bullestock/SmartPendantHardware/kicad/frame.scad

difference(){ translate([0, 0, -0.995]) linear_extrude(height=2.6) polygon(points=[[-44.378709539066506, -47.255384540973324], [-44.378709539066506, 41.744615459026676], [110.6212904609335, 41.744615459026676], [110.6212904609335, -47.255384540973324]]); 
union() {
 linear_extrude(height=10) offset(r=0.1) polygon(points=[[34.621290460933494, 26.744615459026676], [34.621595070620714, 26.70971064615211], [34.6225088068953, 26.674816465621674], [34.62403139142435, 26.639943546540785], [34.62616236041384, 26.605102511538426], [34.62890106475001, 26.57030397353136], [34.632246670196935, 26.535558532491372], [34.63619815765085, 26.50087677221638], [34.64075432345035, 26.466269257106546], [34.64591377974321, 26.431746528946213], [34.65167495490908, 26.397319103692816], [34.65803609403815, 26.362997468273583], [34.66499525946588, 26.328792077391157], [34.67255033136303, 26.294713350338945], [34.68069900838151, 26.260771667827342], [34.68943880835536, 26.226977368821636], [34.698767069056856, 26.193340747392675], [34.70868094900743, 26.159872049581203], [34.71917742834319, 26.126581470276783], [34.73025330973485, 26.093479150112366], [34.74190521936168, 26.060575172375337], [34.75412960793909, 26.027879559936075], [34.76692275179991, 25.995402272194852], [34.78028075402861, 25.963153202048126], [34.7941995456483, 25.931142172875077], [34.80867488686019, 25.89937893554528], [34.82370236833515, 25.867873165448522], [34.839277412556754, 25.836634459547582], [34.85539527521564, 25.805672333454893], [34.87205104665469, 25.774996218534], [34.889239653364626, 25.744615459026676], [34.90695585952926, 25.714539309206565], [34.92519426862063, 25.68477693056027], [34.94394932504264, 25.65533738899662], [34.96321531582342, 25.62622965208518], [34.9829863723555, 25.597462586324582], [35.00325647218361, 25.56904495444173], [35.02401944083891, 25.540985412722577], [35.04526895372004, 25.513292508375358], [35.06699853801956, 25.485974676927], [35.08920157469555, 25.459040239653596], [35.11187130048796, 25.43249740104566], [35.13500080997869, 25.406354246308958], [35.158583057695154, 25.38061873890168], [35.182610860256204, 25.355298718108685], [35.20707689856039, 25.330401896653584], [35.2319737200155, 25.305935858349372], [35.25729374080851, 25.281908055788335], [35.28302924821577, 25.258325808071888], [35.30917240295247, 25.23519629858113], [35.33571524156042, 25.21252657278872], [35.36264967883383, 25.190323536112736], [35.38996751028219, 25.16859395181323], [35.41766041462941, 25.147344438932087], [35.44571995634854, 25.126581470276783], [35.4741375882314, 25.106311370448694], [35.502904653992005, 25.086540313916593], [35.532012390903446, 25.067274323135827], [35.561451932467094, 25.048519266713825], [35.59121431111339, 25.03028085762245], [35.621290460933494, 25.0125646514578], [35.65167122044082, 24.995376044747886], [35.682347335361726, 24.978720273308824], [35.7133094614544, 24.962602410649943], [35.74454816735533, 24.947027366428344], [35.776053937452104, 24.931999884953377], [35.80781717478189, 24.91752454374147], [35.83982820395494, 24.9036057521218], [35.872077274101656, 24.8902477498931], [35.9045545618429, 24.877454606032273], [35.937250174282156, 24.865230217454858], [35.97015415201918, 24.853578307828045], [36.00325647218361, 24.84250242643637], [36.036547051488014, 24.832005947100605], [36.0700157492995, 24.822092067150038], [36.10365237072844, 24.812763806448537], [36.137446669734146, 24.804024006474684], [36.17138835224577, 24.79587532945621], [36.20546707929799, 24.788320257559064], [36.23967247018041, 24.78136109213135], [36.27399410559963, 24.774999953002258], [36.308421530853025, 24.7692387778364], [36.342944259013365, 24.764079321543534], [36.37755177412319, 24.759523155744034], [36.41223353439818, 24.75557166829013], [36.446978975438185, 24.752226062843185], [36.48177751344525, 24.749487358507025], [36.51661854844761, 24.747356389517527], [36.55149146752848, 24.745833804988486], [36.58638564805892, 24.744920068713895], [36.621290460933494, 24.744615459026676], [36.621290460933494, 24.744615459026676], [65.6212904609335, 24.744615459026676], [65.65619527380807, 24.744920068713895], [65.69108945433851, 24.745833804988486], [65.72596237341938, 24.747356389517527], [65.76080340842174, 24.749487358507025], [65.7956019464288, 24.752226062843185], [65.8303473874688, 24.75557166829013], [65.8650291477438, 24.759523155744034], [65.89963666285362, 24.764079321543534], [65.93415939101396, 24.7692387778364], [65.96858681626736, 24.774999953002258], [66.00290845168658, 24.78136109213135], [66.037113842569, 24.788320257559064], [66.07119256962122, 24.79587532945621], [66.10513425213284, 24.804024006474684], [66.13892855113855, 24.812763806448537], [66.17256517256749, 24.822092067150038], [66.20603387037897, 24.832005947100605], [66.23932444968338, 24.84250242643637], [66.27242676984781, 24.853578307828045], [66.30533074758483, 24.865230217454858], [66.33802636002409, 24.877454606032273], [66.37050364776533, 24.8902477498931], [66.40275271791205, 24.9036057521218], [66.4347637470851, 24.91752454374147], [66.46652698441488, 24.931999884953377], [66.49803275451166, 24.947027366428344], [66.52927146041259, 24.962602410649943], [66.56023358650526, 24.978720273308824], [66.59090970142617, 24.995376044747886], [66.6212904609335, 25.0125646514578], [66.6513666107536, 25.03028085762245], [66.6811289893999, 25.048519266713825], [66.71056853096354, 25.067274323135827], [66.73967626787498, 25.086540313916593], [66.76844333363559, 25.106311370448694], [66.79686096551845, 25.126581470276783], [66.82492050723758, 25.147344438932087], [66.8526134115848, 25.16859395181323], [66.87993124303316, 25.190323536112736], [66.90686568030657, 25.21252657278872], [66.93340851891452, 25.23519629858113], [66.95955167365122, 25.258325808071888], [66.98528718105848, 25.281908055788335], [67.01060720185149, 25.305935858349372], [67.0355040233066, 25.330401896653584], [67.05997006161078, 25.355298718108678], [67.08399786417183, 25.38061873890168], [67.1075801118883, 25.406354246308958], [67.13070962137903, 25.43249740104566], [67.15337934717144, 25.459040239653596], [67.17558238384743, 25.485974676927], [67.19731196814695, 25.513292508375358], [67.21856148102808, 25.540985412722577], [67.23932444968338, 25.56904495444173], [67.25959454951149, 25.597462586324582], [67.27936560604357, 25.62622965208518], [67.29863159682435, 25.65533738899662], [67.31738665324636, 25.68477693056027], [67.33562506233773, 25.714539309206565], [67.35334126850236, 25.744615459026676], [67.3705298752123, 25.774996218534], [67.38718564665135, 25.805672333454893], [67.40330350931023, 25.836634459547582], [67.41887855353184, 25.867873165448522], [67.4339060350068, 25.89937893554528], [67.44838137621869, 25.931142172875077], [67.46230016783838, 25.963153202048126], [67.47565817006708, 25.995402272194852], [67.4884513139279, 26.027879559936075], [67.5006757025053, 26.060575172375337], [67.51232761213214, 26.093479150112366], [67.5234034935238, 26.126581470276783], [67.53389997285956, 26.159872049581203], [67.54381385281013, 26.193340747392675], [67.55314211351163, 26.226977368821636], [67.56188191348548, 26.260771667827342], [67.57003059050396, 26.294713350338945], [67.5775856624011, 26.328792077391157], [67.58454482782884, 26.362997468273583], [67.5909059669579, 26.397319103692816], [67.59666714212378, 26.431746528946213], [67.60182659841664, 26.466269257106546], [67.60638276421614, 26.50087677221638], [67.61033425167005, 26.535558532491372], [67.61367985711698, 26.57030397353136], [67.61641856145314, 26.605102511538426], [67.61854953044264, 26.639943546540785], [67.62007211497169, 26.674816465621674], [67.62098585124627, 26.70971064615211], [67.6212904609335, 26.744615459026676], [67.6212904609335, 26.744615459026676], [93.6212904609335, 26.744615459026676], [93.65619527380807, 26.744310849339456], [93.69108945433851, 26.743397113064866], [93.72596237341938, 26.741874528535824], [93.76080340842174, 26.739743559546326], [93.7956019464288, 26.737004855210166], [93.8303473874688, 26.73365924976322], [93.8650291477438, 26.729707762309317], [93.89963666285362, 26.725151596509818], [93.93415939101396, 26.719992140216952], [93.96858681626736, 26.714230965051094], [94.00290845168658, 26.707869825922003], [94.037113842569, 26.700910660494287], [94.07119256962122, 26.693355588597143], [94.10513425213284, 26.685206911578668], [94.13892855113855, 26.676467111604815], [94.17256517256749, 26.667138850903314], [94.20603387037897, 26.657224970952747], [94.23932444968338, 26.646728491616983], [94.27242676984781, 26.635652610225307], [94.30533074758483, 26.624000700598494], [94.33802636002409, 26.611776312021078], [94.37050364776533, 26.598983168160252], [94.40275271791205, 26.585625165931553], [94.4347637470851, 26.57170637431188], [94.46652698441488, 26.557231033099974], [94.49803275451166, 26.542203551625008], [94.52927146041259, 26.52662850740341], [94.56023358650526, 26.510510644744528], [94.59090970142617, 26.493854873305466], [94.6212904609335, 26.47666626659555], [94.6513666107536, 26.4589500604309], [94.6811289893999, 26.440711651339527], [94.71056853096354, 26.421956594917525], [94.73967626787498, 26.402690604136758], [94.76844333363559, 26.382919547604658], [94.79686096551845, 26.36264944777657], [94.82492050723758, 26.341886479121264], [94.8526134115848, 26.320636966240123], [94.87993124303316, 26.298907381940616], [94.90686568030657, 26.276704345264633], [94.93340851891452, 26.254034619472222], [94.95955167365122, 26.230905109981464], [94.98528718105848, 26.207322862265016], [95.01060720185149, 26.18329505970398], [95.0355040233066, 26.158829021399768], [95.05997006161078, 26.133932199944674], [95.08399786417183, 26.10861217915167], [95.1075801118883, 26.082876671744394], [95.13070962137903, 26.056733517007693], [95.15337934717144, 26.030190678399755], [95.17558238384743, 26.00325624112635], [95.19731196814695, 25.975938409677994], [95.21856148102808, 25.948245505330775], [95.23932444968338, 25.920185963611623], [95.25959454951149, 25.89176833172877], [95.27936560604357, 25.863001265968173], [95.29863159682435, 25.83389352905673], [95.31738665324636, 25.804453987493083], [95.33562506233773, 25.774691608846787], [95.35334126850236, 25.744615459026676], [95.3705298752123, 25.714234699519352], [95.38718564665135, 25.683558584598458], [95.40330350931023, 25.65259645850577], [95.41887855353184, 25.62135775260483], [95.4339060350068, 25.589851982508073], [95.44838137621869, 25.558088745178274], [95.46230016783838, 25.526077716005226], [95.47565817006708, 25.4938286458585], [95.4884513139279, 25.461351358117277], [95.5006757025053, 25.428655745678014], [95.51232761213214, 25.395751767940986], [95.5234034935238, 25.36264944777657], [95.53389997285956, 25.32935886847215], [95.54381385281013, 25.295890170660677], [95.55314211351163, 25.262253549231716], [95.56188191348548, 25.22845925022601], [95.57003059050396, 25.194517567714406], [95.5775856624011, 25.160438840662195], [95.58454482782884, 25.126233449779768], [95.5909059669579, 25.091911814360536], [95.59666714212378, 25.057484389107138], [95.60182659841664, 25.022961660946805], [95.60638276421614, 24.988354145836972], [95.61033425167005, 24.95367238556198], [95.61367985711698, 24.918926944521992], [95.61641856145314, 24.884128406514925], [95.61854953044264, 24.849287371512567], [95.62007211497169, 24.814414452431677], [95.62098585124627, 24.77952027190124], [95.6212904609335, 24.744615459026676], [95.6212904609335, 24.744615459026676], [95.6212904609335, -8.255384540973324], [95.62098585124627, -8.290289353847896], [95.62007211497169, -8.325183534378326], [95.61854953044264, -8.360056453459208], [95.61641856145314, -8.39489748846158], [95.61367985711698, -8.429696026468648], [95.61033425167005, -8.464441467508635], [95.60638276421614, -8.499123227783613], [95.60182659841664, -8.533730742893454], [95.59666714212378, -8.56825347105378], [95.5909059669579, -8.602680896307191], [95.58454482782884, -8.63700253172641], [95.5775856624011, -8.671207922608843], [95.57003059050396, -8.705286649661048], [95.56188191348548, -8.739228332172658], [95.55314211351163, -8.773022631178364], [95.54381385281013, -8.806659252607318], [95.53389997285956, -8.840127950418804], [95.5234034935238, -8.873418529723224], [95.51232761213214, -8.906520849887642], [95.5006757025053, -8.939424827624663], [95.4884513139279, -8.972120440063918], [95.47565817006708, -9.004597727805148], [95.46230016783838, -9.036846797951867], [95.44838137621869, -9.06885782712493], [95.4339060350068, -9.100621064454728], [95.41887855353184, -9.132126834551485], [95.40330350931023, -9.163365540452418], [95.38718564665135, -9.194327666545107], [95.3705298752123, -9.225003781466], [95.35334126850236, -9.255384540973324], [95.33562506233773, -9.285460690793428], [95.31738665324636, -9.315223069439739], [95.29863159682435, -9.344662611003372], [95.27936560604357, -9.373770347914814], [95.25959454951149, -9.402537413675418], [95.23932444968338, -9.430955045558264], [95.21856148102808, -9.459014587277423], [95.19731196814695, -9.486707491624642], [95.17558238384743, -9.514025323073], [95.15337934717144, -9.540959760346396], [95.13070962137903, -9.567502598954334], [95.1075801118883, -9.593645753691035], [95.08399786417183, -9.619381261098326], [95.05997006161078, -9.644701281891315], [95.0355040233066, -9.669598103346416], [95.01060720185149, -9.694064141650628], [94.98528718105848, -9.718091944211665], [94.95955167365122, -9.741674191928112], [94.93340851891452, -9.76480370141887], [94.90686568030657, -9.787473427211282], [94.87993124303316, -9.809676463887271], [94.8526134115848, -9.831406048186764], [94.82492050723758, -9.852655561067905], [94.79686096551845, -9.873418529723224], [94.76844333363559, -9.893688629551306], [94.73967626787498, -9.913459686083414], [94.71056853096354, -9.932725676864166], [94.6811289893999, -9.951480733286175], [94.6513666107536, -9.969719142377542], [94.6212904609335, -9.987435348542206], [94.59090970142617, -10.004623955252114], [94.56023358650526, -10.021279726691176], [94.52927146041259, -10.037397589350064], [94.49803275451166, -10.052972633571656], [94.46652698441488, -10.06800011504663], [94.4347637470851, -10.082475456258521], [94.40275271791205, -10.096394247878209], [94.37050364776533, -10.109752250106894], [94.33802636002409, -10.122545393967727], [94.30533074758483, -10.134769782545135], [94.27242676984781, -10.146421692171955], [94.23932444968338, -10.157497573563631], [94.20603387037897, -10.167994052899388], [94.17256517256749, -10.177907932849962], [94.13892855113855, -10.187236193551456], [94.10513425213284, -10.195975993525323], [94.07119256962122, -10.204124670543791], [94.037113842569, -10.211679742440936], [94.00290845168658, -10.218638907868652], [93.96858681626736, -10.225000046997735], [93.93415939101396, -10.230761222163594], [93.89963666285362, -10.235920678456466], [93.8650291477438, -10.240476844255966], [93.8303473874688, -10.24442833170987], [93.7956019464288, -10.247773937156822], [93.76080340842174, -10.250512641492975], [93.72596237341938, -10.252643610482465], [93.69108945433851, -10.254166195011521], [93.65619527380807, -10.255079931286105], [93.6212904609335, -10.255384540973324], [93.6212904609335, -10.255384540973324], [93.6212904609335, -30.255384540973324], [93.62098585124627, -30.290289353847896], [93.62007211497169, -30.325183534378326], [93.61854953044264, -30.360056453459208], [93.61641856145314, -30.39489748846158], [93.61367985711698, -30.429696026468648], [93.61033425167005, -30.464441467508635], [93.60638276421614, -30.499123227783613], [93.60182659841664, -30.533730742893454], [93.59666714212378, -30.56825347105378], [93.5909059669579, -30.60268089630719], [93.58454482782884, -30.63700253172641], [93.5775856624011, -30.671207922608843], [93.57003059050396, -30.705286649661048], [93.56188191348548, -30.739228332172658], [93.55314211351163, -30.773022631178364], [93.54381385281013, -30.806659252607318], [93.53389997285956, -30.840127950418804], [93.5234034935238, -30.873418529723224], [93.51232761213214, -30.90652084988764], [93.5006757025053, -30.939424827624663], [93.4884513139279, -30.972120440063918], [93.47565817006708, -31.004597727805148], [93.46230016783838, -31.036846797951867], [93.44838137621869, -31.06885782712493], [93.4339060350068, -31.100621064454728], [93.41887855353184, -31.132126834551485], [93.40330350931023, -31.163365540452418], [93.38718564665135, -31.194327666545107], [93.3705298752123, -31.225003781466], [93.35334126850236, -31.255384540973324], [93.33562506233773, -31.28546069079343], [93.31738665324636, -31.31522306943974], [93.29863159682435, -31.344662611003372], [93.27936560604357, -31.373770347914814], [93.25959454951149, -31.402537413675418], [93.23932444968338, -31.430955045558264], [93.21856148102808, -31.459014587277423], [93.19731196814695, -31.486707491624642], [93.17558238384743, -31.514025323073], [93.15337934717144, -31.540959760346396], [93.13070962137903, -31.567502598954334], [93.1075801118883, -31.593645753691035], [93.08399786417183, -31.619381261098326], [93.05997006161078, -31.644701281891315], [93.0355040233066, -31.669598103346416], [93.01060720185149, -31.694064141650628], [92.98528718105848, -31.718091944211665], [92.95955167365122, -31.741674191928112], [92.93340851891452, -31.76480370141887], [92.90686568030657, -31.78747342721128], [92.87993124303316, -31.80967646388727], [92.8526134115848, -31.831406048186764], [92.82492050723758, -31.852655561067905], [92.79686096551845, -31.873418529723224], [92.76844333363559, -31.893688629551306], [92.73967626787498, -31.913459686083414], [92.71056853096354, -31.932725676864166], [92.6811289893999, -31.951480733286175], [92.6513666107536, -31.969719142377542], [92.6212904609335, -31.987435348542206], [92.59090970142617, -32.004623955252114], [92.56023358650526, -32.021279726691176], [92.52927146041259, -32.037397589350064], [92.49803275451166, -32.052972633571656], [92.46652698441488, -32.06800011504663], [92.4347637470851, -32.08247545625852], [92.40275271791205, -32.09639424787821], [92.37050364776533, -32.109752250106894], [92.33802636002409, -32.12254539396773], [92.30533074758483, -32.134769782545135], [92.27242676984781, -32.146421692171955], [92.23932444968338, -32.15749757356363], [92.20603387037897, -32.16799405289939], [92.17256517256749, -32.17790793284996], [92.13892855113855, -32.187236193551456], [92.10513425213284, -32.19597599352532], [92.07119256962122, -32.20412467054379], [92.037113842569, -32.211679742440936], [92.00290845168658, -32.21863890786865], [91.96858681626736, -32.225000046997735], [91.93415939101396, -32.23076122216359], [91.89963666285362, -32.235920678456466], [91.8650291477438, -32.240476844255966], [91.8303473874688, -32.24442833170987], [91.7956019464288, -32.24777393715682], [91.76080340842174, -32.250512641492975], [91.72596237341938, -32.252643610482465], [91.69108945433851, -32.25416619501152], [91.65619527380807, -32.255079931286105], [91.6212904609335, -32.255384540973324], [91.6212904609335, -32.255384540973324], [67.6212904609335, -32.255384540973324], [67.62098585124627, -32.22047972809875], [67.62007211497169, -32.18558554756832], [67.61854953044264, -32.15071262848744], [67.61641856145314, -32.11587159348507], [67.61367985711698, -32.081073055478], [67.61033425167005, -32.04632761443801], [67.60638276421614, -32.011645854163035], [67.60182659841664, -31.977038339053195], [67.59666714212378, -31.94251561089287], [67.5909059669579, -31.908088185639457], [67.58454482782884, -31.87376655022024], [67.5775856624011, -31.839561159337805], [67.57003059050396, -31.8054824322856], [67.56188191348548, -31.77154074977399], [67.55314211351163, -31.737746450768284], [67.54381385281013, -31.70410982933933], [67.53389997285956, -31.670641131527844], [67.5234034935238, -31.637350552223424], [67.51232761213214, -31.604248232059007], [67.5006757025053, -31.571344254321986], [67.4884513139279, -31.53864864188273], [67.47565817006708, -31.5061713541415], [67.46230016783838, -31.47392228399478], [67.44838137621869, -31.44191125482172], [67.4339060350068, -31.41014801749192], [67.41887855353184, -31.378642247395163], [67.40330350931023, -31.34740354149423], [67.38718564665135, -31.316441415401542], [67.3705298752123, -31.285765300480648], [67.35334126850236, -31.255384540973324], [67.33562506233773, -31.22530839115322], [67.31738665324636, -31.19554601250691], [67.29863159682435, -31.166106470943276], [67.27936560604357, -31.136998734031835], [67.25959454951149, -31.10823166827123], [67.23932444968338, -31.079814036388385], [67.21856148102808, -31.051754494669225], [67.19731196814695, -31.024061590322006], [67.17558238384743, -30.99674375887365], [67.15337934717144, -30.969809321600252], [67.13070962137903, -30.943266482992314], [67.1075801118883, -30.917123328255613], [67.08399786417183, -30.891387820848323], [67.05997006161078, -30.866067800055333], [67.0355040233066, -30.841170978600232], [67.01060720185149, -30.81670494029602], [66.98528718105848, -30.792677137734984], [66.95955167365122, -30.769094890018536], [66.93340851891452, -30.745965380527778], [66.90686568030657, -30.723295654735367], [66.87993124303316, -30.701092618059377], [66.8526134115848, -30.679363033759884], [66.82492050723758, -30.658113520878743], [66.79686096551845, -30.637350552223424], [66.76844333363559, -30.617080452395342], [66.73967626787498, -30.597309395863235], [66.71056853096354, -30.578043405082482], [66.6811289893999, -30.559288348660473], [66.6513666107536, -30.541049939569106], [66.6212904609335, -30.523333733404442], [66.59090970142617, -30.506145126694534], [66.56023358650526, -30.489489355255472], [66.52927146041259, -30.473371492596584], [66.49803275451166, -30.457796448374992], [66.46652698441488, -30.44276896690002], [66.4347637470851, -30.428293625688127], [66.40275271791205, -30.41437483406844], [66.37050364776533, -30.401016831839755], [66.33802636002409, -30.388223687978922], [66.30533074758483, -30.375999299401514], [66.27242676984781, -30.364347389774693], [66.23932444968338, -30.353271508383017], [66.20603387037897, -30.34277502904726], [66.17256517256749, -30.332861149096686], [66.13892855113855, -30.323532888395192], [66.10513425213284, -30.314793088421325], [66.07119256962122, -30.306644411402857], [66.037113842569, -30.299089339505713], [66.00290845168658, -30.292130174077997], [65.96858681626736, -30.285769034948913], [65.93415939101396, -30.280007859783055], [65.89963666285362, -30.274848403490182], [65.8650291477438, -30.270292237690683], [65.8303473874688, -30.26634075023678], [65.7956019464288, -30.262995144789826], [65.76080340842174, -30.260256440453674], [65.72596237341938, -30.258125471464183], [65.69108945433851, -30.256602886935127], [65.65619527380807, -30.255689150660544], [65.6212904609335, -30.255384540973324], [65.6212904609335, -30.255384540973324], [36.621290460933494, -30.255384540973324], [36.58638564805892, -30.255689150660544], [36.55149146752848, -30.256602886935127], [36.51661854844761, -30.258125471464183], [36.48177751344525, -30.260256440453674], [36.446978975438185, -30.262995144789826], [36.41223353439818, -30.26634075023678], [36.37755177412319, -30.270292237690683], [36.342944259013365, -30.274848403490182], [36.308421530853025, -30.280007859783055], [36.27399410559963, -30.285769034948913], [36.23967247018041, -30.292130174077997], [36.20546707929799, -30.299089339505713], [36.17138835224577, -30.306644411402857], [36.137446669734146, -30.314793088421325], [36.10365237072844, -30.323532888395192], [36.0700157492995, -30.332861149096686], [36.036547051488014, -30.34277502904726], [36.00325647218361, -30.353271508383017], [35.97015415201918, -30.364347389774693], [35.937250174282156, -30.375999299401514], [35.9045545618429, -30.388223687978922], [35.872077274101656, -30.401016831839755], [35.83982820395494, -30.41437483406844], [35.80781717478189, -30.428293625688127], [35.776053937452104, -30.44276896690002], [35.74454816735533, -30.457796448374992], [35.7133094614544, -30.473371492596584], [35.682347335361726, -30.489489355255472], [35.65167122044082, -30.506145126694534], [35.621290460933494, -30.523333733404442], [35.59121431111339, -30.541049939569106], [35.561451932467094, -30.559288348660473], [35.532012390903446, -30.578043405082482], [35.502904653992005, -30.597309395863235], [35.4741375882314, -30.617080452395342], [35.44571995634854, -30.637350552223424], [35.41766041462941, -30.658113520878743], [35.38996751028219, -30.679363033759884], [35.36264967883383, -30.701092618059377], [35.33571524156042, -30.723295654735367], [35.30917240295247, -30.745965380527778], [35.28302924821577, -30.769094890018536], [35.25729374080851, -30.792677137734984], [35.2319737200155, -30.81670494029602], [35.20707689856039, -30.841170978600232], [35.182610860256204, -30.866067800055333], [35.158583057695154, -30.891387820848323], [35.13500080997869, -30.917123328255613], [35.11187130048796, -30.943266482992314], [35.08920157469555, -30.969809321600252], [35.06699853801956, -30.99674375887365], [35.04526895372004, -31.024061590322006], [35.02401944083891, -31.051754494669225], [35.00325647218361, -31.079814036388385], [34.9829863723555, -31.10823166827123], [34.96321531582342, -31.136998734031835], [34.94394932504264, -31.166106470943276], [34.92519426862063, -31.19554601250691], [34.90695585952926, -31.22530839115322], [34.889239653364626, -31.255384540973324], [34.87205104665469, -31.285765300480648], [34.85539527521564, -31.316441415401542], [34.839277412556754, -31.34740354149423], [34.82370236833515, -31.378642247395163], [34.80867488686019, -31.41014801749192], [34.7941995456483, -31.44191125482172], [34.78028075402861, -31.47392228399478], [34.76692275179991, -31.5061713541415], [34.75412960793909, -31.53864864188273], [34.74190521936168, -31.571344254321986], [34.73025330973485, -31.604248232059007], [34.71917742834319, -31.637350552223424], [34.70868094900743, -31.670641131527844], [34.698767069056856, -31.70410982933933], [34.68943880835536, -31.737746450768284], [34.68069900838151, -31.77154074977399], [34.67255033136303, -31.8054824322856], [34.66499525946588, -31.839561159337805], [34.65803609403815, -31.87376655022024], [34.65167495490908, -31.908088185639457], [34.64591377974321, -31.94251561089287], [34.64075432345035, -31.977038339053195], [34.63619815765085, -32.011645854163035], [34.632246670196935, -32.04632761443801], [34.62890106475001, -32.081073055478], [34.62616236041384, -32.11587159348507], [34.62403139142435, -32.15071262848744], [34.6225088068953, -32.18558554756832], [34.621595070620714, -32.22047972809875], [34.621290460933494, -32.255384540973324], [34.621290460933494, -32.255384540973324], [-27.378709539066506, -32.255384540973324], [-27.413614351941078, -32.255079931286105], [-27.448508532471507, -32.25416619501152], [-27.48338145155239, -32.252643610482465], [-27.518222486554762, -32.250512641492975], [-27.55302102456183, -32.24777393715682], [-27.587766465601817, -32.24442833170987], [-27.622448225876795, -32.240476844255966], [-27.657055740986635, -32.235920678456466], [-27.69157846914696, -32.23076122216359], [-27.726005894400373, -32.225000046997735], [-27.76032752981959, -32.21863890786865], [-27.794532920702025, -32.211679742440936], [-27.82861164775423, -32.20412467054379], [-27.86255333026584, -32.19597599352532], [-27.896347629271546, -32.187236193551456], [-27.9299842507005, -32.17790793284996], [-27.963452948511986, -32.16799405289939], [-27.996743527816406, -32.15749757356363], [-28.029845847980823, -32.146421692171955], [-28.062749825717844, -32.134769782545135], [-28.0954454381571, -32.12254539396773], [-28.12792272589833, -32.109752250106894], [-28.16017179604505, -32.09639424787821], [-28.19218282521811, -32.08247545625852], [-28.22394606254791, -32.06800011504663], [-28.255451832644667, -32.052972633571656], [-28.2866905385456, -32.037397589350064], [-28.31765266463829, -32.021279726691176], [-28.348328779559182, -32.004623955252114], [-28.378709539066506, -31.987435348542206], [-28.40878568888661, -31.969719142377542], [-28.43854806753292, -31.951480733286175], [-28.467987609096554, -31.932725676864166], [-28.497095346007995, -31.913459686083414], [-28.5258624117686, -31.893688629551306], [-28.554280043651445, -31.873418529723224], [-28.582339585370605, -31.852655561067905], [-28.610032489717824, -31.831406048186764], [-28.63735032116618, -31.80967646388727], [-28.664284758439578, -31.78747342721128], [-28.690827597047516, -31.76480370141887], [-28.716970751784217, -31.741674191928112], [-28.742706259191507, -31.718091944211665], [-28.768026279984497, -31.694064141650628], [-28.792923101439598, -31.669598103346416], [-28.81738913974381, -31.644701281891315], [-28.841416942304846, -31.619381261098326], [-28.864999190021294, -31.593645753691035], [-28.888128699512052, -31.567502598954334], [-28.910798425304463, -31.540959760346396], [-28.933001461980453, -31.514025323073], [-28.954731046279946, -31.486707491624642], [-28.975980559161087, -31.459014587277423], [-28.996743527816406, -31.430955045558264], [-29.017013627644488, -31.402537413675418], [-29.036784684176595, -31.373770347914814], [-29.056050674957348, -31.344662611003372], [-29.074805731379357, -31.31522306943974], [-29.093044140470724, -31.28546069079343], [-29.110760346635388, -31.255384540973324], [-29.127948953345296, -31.225003781466], [-29.144604724784358, -31.194327666545107], [-29.160722587443246, -31.163365540452418], [-29.176297631664838, -31.132126834551485], [-29.19132511313981, -31.100621064454728], [-29.205800454351703, -31.06885782712493], [-29.21971924597139, -31.036846797951867], [-29.233077248200075, -31.004597727805148], [-29.245870392060908, -30.972120440063918], [-29.258094780638316, -30.939424827624663], [-29.269746690265137, -30.90652084988764], [-29.280822571656813, -30.873418529723224], [-29.29131905099257, -30.840127950418804], [-29.301232930943144, -30.806659252607318], [-29.310561191644638, -30.773022631178364], [-29.319300991618505, -30.739228332172658], [-29.327449668636973, -30.705286649661048], [-29.335004740534117, -30.671207922608843], [-29.341963905961833, -30.63700253172641], [-29.348325045090917, -30.60268089630719], [-29.354086220256775, -30.56825347105378], [-29.359245676549648, -30.533730742893454], [-29.363801842349147, -30.499123227783613], [-29.36775332980305, -30.464441467508635], [-29.371098935250004, -30.429696026468648], [-29.373837639586156, -30.39489748846158], [-29.375968608575647, -30.360056453459208], [-29.377491193104703, -30.325183534378326], [-29.378404929379286, -30.290289353847896], [-29.378709539066506, -30.255384540973324], [-29.378709539066506, -30.255384540973324], [-29.377049539066505, -24.25501454097332], [-29.36661253906651, -24.25264454097332], [-29.3512215390665, -24.24907854097333], [-29.3327375390665, -24.244718540973324], [-29.31197453906651, -24.23974454097332], [-29.28939953906651, -24.23425854097333], [-29.26531953906651, -24.22832554097333], [-29.2399495390665, -24.221996540973322], [-29.21345253906651, -24.21530554097332], [-29.185957539066507, -24.20828254097333], [-29.15756553906651, -24.200949540973326], [-29.1283625390665, -24.19332554097332], [-29.098419539066512, -24.185427540973322], [-29.067797539066504, -24.177269540973327], [-29.0365485390665, -24.16886354097332], [-29.0047195390665, -24.16021954097333], [-28.97235153906651, -24.15134654097332], [-28.93947953906651, -24.142254540973326], [-28.90613653906651, -24.132950540973326], [-28.87235253906651, -24.123441540973317], [-28.83815353906651, -24.113733540973328], [-28.8035645390665, -24.10383254097333], [-28.76860653906651, -24.09374354097332], [-28.733300539066505, -24.083472540973318], [-28.697665539066506, -24.073022540973326], [-28.66171953906651, -24.06239954097333], [-28.62547753906651, -24.051606540973324], [-28.588955539066504, -24.040646540973327], [-28.552167539066502, -24.029524540973327], [-28.515125539066503, -24.01824354097333], [-28.47784453906651, -24.00680654097333], [-28.4403335390665, -23.99521554097332], [-28.402604539066502, -23.98347454097332], [-28.364667539066502, -23.971585540973322], [-28.326533539066503, -23.95955254097332], [-28.28821053906651, -23.947375540973326], [-28.249707539066506, -23.93505854097333], [-28.211032539066508, -23.922603540973327], [-28.17219453906651, -23.910012540973327], [-28.133200539066507, -23.897287540973323], [-28.09405753906651, -23.88442954097333], [-28.054772539066505, -23.87144254097332], [-28.0153515390665, -23.858325540973325], [-27.97580153906651, -23.84508354097332], [-27.9361285390665, -23.83171554097332], [-27.896337539066508, -23.81822354097332], [-27.856434539066512, -23.80461054097333], [-27.816424539066503, -23.79087654097333], [-27.776313539066507, -23.77702454097333], [-27.736104539066503, -23.76305454097333], [-27.6958045390665, -23.748967540973325], [-27.65541553906651, -23.734766540973325], [-27.614943539066502, -23.72045154097333], [-27.57439253906651, -23.70602454097333], [-27.533766539066505, -23.691485540973318], [-27.4930685390665, -23.676837540973324], [-27.452303539066506, -23.66208054097332], [-27.411473539066506, -23.64721554097332], [-27.3705835390665, -23.63224354097332], [-27.3296365390665, -23.617165540973318], [-27.288635539066505, -23.601983540973322], [-27.24758353906651, -23.58669854097333], [-27.20648453906651, -23.571309540973317], [-27.165339539066508, -23.555819540973317], [-27.124153539066512, -23.54022854097333], [-27.0829285390665, -23.524538540973325], [-27.04166653906651, -23.50874854097333], [-27.00037053906651, -23.492860540973325], [-26.9590435390665, -23.476875540973325], [-26.917687539066506, -23.460793540973327], [-26.876305539066507, -23.44461554097333], [-26.8348985390665, -23.42834354097333], [-26.793470539066504, -23.411976540973328], [-26.752021539066504, -23.39551654097332], [-26.710555539066505, -23.378964540973328], [-26.6690745390665, -23.362319540973317], [-26.627579539066502, -23.345583540973323], [-26.586072539066507, -23.328757540973328], [-26.544555539066508, -23.31184154097332], [-26.503031539066512, -23.29483654097332], [-26.461501539066504, -23.27774254097332], [-26.419966539066507, -23.26056054097333], [-26.378428539066505, -23.24329154097333], [-26.336890539066502, -23.225935540973325], [-26.2953525390665, -23.208493540973322], [-26.253817539066517, -23.19096654097332], [-26.2122855390665, -23.17335454097332], [-26.170758539066497, -23.15565854097332], [-26.129239539066504, -23.13787754097332], [-26.087727539066492, -23.12001454097333], [-26.046225539066512, -23.10206854097332], [-26.004734539066504, -23.08404054097332], [-25.963255539066495, -23.065931540973324], [-25.92178953906651, -23.047740540973322], [-25.880338539066514, -23.029469540973324], [-25.838904539066505, -23.011118540973328], [-25.79748653906651, -22.99268854097332], [-25.7560875390665, -22.974178540973327], [-25.714707539066495, -22.95559054097332], [-25.673348539066495, -22.936924540973322], [-25.632011539066497, -22.918180540973324], [-25.5906965390665, -22.89935954097332], [-25.549406539066496, -22.88046154097333], [-25.508140539066517, -22.86148754097333], [-25.4669005390665, -22.84243854097332], [-25.4256875390665, -22.82331354097333], [-25.384502539066517, -22.80411354097332], [-25.34334553906652, -22.784838540973325], [-25.3022195390665, -22.76548954097332], [-25.26112253906652, -22.74606754097333], [-25.220057539066516, -22.726571540973325], [-25.179025539066515, -22.707003540973318], [-25.13802553906652, -22.687361540973328], [-25.09706053906652, -22.667648540973317], [-25.056129539066518, -22.64786354097332], [-25.015233539066514, -22.62800754097333], [-24.974374539066503, -22.60808054097332], [-24.93355253906651, -22.588082540973318], [-24.89276853906651, -22.568013540973325], [-24.852022539066496, -22.547875540973322], [-24.8113155390665, -22.527667540973326], [-24.770648539066514, -22.50739154097333], [-24.73002253906651, -22.487045540973327], [-24.689437539066518, -22.466630540973327], [-24.648894539066504, -22.446148540973326], [-24.608393539066498, -22.425598540973326], [-24.567935539066497, -22.404980540973327], [-24.5275215390665, -22.384295540973326], [-24.4871525390665, -22.363543540973325], [-24.446827539066504, -22.34272454097332], [-24.406548539066506, -22.32183954097333], [-24.366315539066505, -22.30088954097333], [-24.326128539066502, -22.27987254097333], [-24.285988539066494, -22.25879154097332], [-24.245896539066507, -22.23764454097332], [-24.205852539066512, -22.21643254097333], [-24.165857539066508, -22.19515654097333], [-24.125911539066493, -22.17381654097332], [-24.086015539066494, -22.15241254097333], [-24.046168539066514, -22.13094554097333], [-24.006373539066516, -22.10941454097332], [-23.966628539066505, -22.087820540973325], [-23.926935539066505, -22.06616354097332], [-23.88729353906652, -22.04444354097332], [-23.847704539066513, -22.02266254097333], [-23.808168539066514, -22.000818540973327], [-23.768685539066496, -21.978913540973323], [-23.729256539066512, -21.95694654097332], [-23.689880539066507, -21.934918540973328], [-23.650559539066506, -21.91282954097332], [-23.61129353906651, -21.890679540973323], [-23.572082539066514, -21.868469540973322], [-23.532926539066494, -21.84619954097333], [-23.493826539066504, -21.823868540973322], [-23.454782539066514, -21.80147854097332], [-23.415795539066494, -21.779029540973326], [-23.3768655390665, -21.756520540973327], [-23.337991539066508, -21.73395254097332], [-23.299176539066508, -21.71132554097332], [-23.260418539066507, -21.688639540973327], [-23.2217195390665, -21.66589654097332], [-23.183078539066514, -21.643094540973323], [-23.144495539066497, -21.62023454097333], [-23.1059725390665, -21.597316540973324], [-23.067508539066495, -21.57434154097332], [-23.02910453906651, -21.55130954097332], [-22.990759539066516, -21.528219540973325], [-22.952475539066512, -21.505073540973328], [-22.9142515390665, -21.48187054097332], [-22.8760885390665, -21.458610540973325], [-22.837986539066492, -21.43529454097333], [-22.7999455390665, -21.41192354097332], [-22.761966539066492, -21.388495540973324], [-22.7240485390665, -21.365011540973327], [-22.686193539066494, -21.341472540973328], [-22.648399539066503, -21.317878540973325], [-22.610668539066495, -21.29422954097332], [-22.5729995390665, -21.270525540973324], [-22.53539353906652, -21.246766540973326], [-22.49785053906652, -21.222952540973324], [-22.4603715390665, -21.19908554097333], [-22.422955539066493, -21.17516354097333], [-22.385602539066497, -21.151187540973325], [-22.348314539066507, -21.12715754097333], [-22.3110895390665, -21.103073540973327], [-22.2739295390665, -21.07893654097333], [-22.23683353906651, -21.054746540973326], [-22.1998015390665, -21.030503540973328], [-22.162835539066492, -21.006206540973324], [-22.125933539066494, -20.981857540973323], [-22.089096539066503, -20.957455540973328], [-22.052325539066516, -20.933001540973322], [-22.015619539066506, -20.908494540973322], [-21.9789795390665, -20.883935540973326], [-21.9424045390665, -20.85932554097333], [-21.905896539066504, -20.834662540973326], [-21.869453539066512, -20.809948540973323], [-21.833077539066494, -20.785182540973324], [-21.79676653906651, -20.760365540973325], [-21.760523539066497, -20.73549654097333], [-21.724346539066516, -20.71057754097332], [-21.68823553906651, -20.685606540973325], [-21.652192539066505, -20.66058554097333], [-21.616215539066502, -20.63551354097332], [-21.5803065390665, -20.610391540973325], [-21.544464539066496, -20.58521854097333], [-21.508689539066495, -20.55999554097332], [-21.472982539066493, -20.53472254097332], [-21.437342539066492, -20.509400540973317], [-21.40177053906652, -20.48402754097333], [-21.366266539066515, -20.458604540973326], [-21.33083053906651, -20.43313354097333], [-21.29546153906651, -20.40761154097332], [-21.2601615390665, -20.38204154097332], [-21.224929539066494, -20.35642154097333], [-21.189765539066514, -20.33075254097332], [-21.1546705390665, -20.30503554097332], [-21.119643539066516, -20.27926854097332], [-21.0846855390665, -20.253453540973325], [-21.049796539066506, -20.227590540973324], [-21.014975539066512, -20.20167854097332], [-20.980223539066515, -20.17571854097332], [-20.945540539066513, -20.14971054097333], [-20.91092653906651, -20.123653540973322], [-20.8763815390665, -20.09754954097332], [-20.841905539066516, -20.071397540973322], [-20.807499539066498, -20.04519754097332], [-20.773161539066507, -20.01895054097332], [-20.73889353906651, -19.99265654097333], [-20.704695539066506, -19.96631454097333], [-20.6705665390665, -19.939924540973323], [-20.636506539066517, -19.91348854097332], [-20.602517539066497, -19.88700554097332], [-20.568596539066505, -19.86047454097333], [-20.534746539066504, -19.833897540973325], [-20.5009655390665, -19.807274540973324], [-20.467255539066514, -19.78060354097333], [-20.433614539066497, -19.753887540973324], [-20.400043539066502, -19.727123540973324], [-20.3665425390665, -19.700314540973324], [-20.333111539066493, -19.67345854097333], [-20.29975053906651, -19.64655654097332], [-20.266459539066517, -19.61960954097333], [-20.233239539066517, -19.592615540973327], [-20.20008953906651, -19.565576540973325], [-20.1670095390665, -19.538491540973325], [-20.133999539066508, -19.511360540973328], [-20.10106053906651, -19.48418454097333], [-20.068191539066504, -19.456962540973322], [-20.035392539066493, -19.429695540973327], [-20.0026645390665, -19.402383540973318], [-19.9700075390665, -19.375025540973326], [-19.937420539066494, -19.34762354097333], [-19.90490353906651, -19.32017654097332], [-19.872457539066517, -19.29268354097333], [-19.840082539066515, -19.26514654097332], [-19.807777539066507, -19.237564540973324], [-19.77554353906652, -19.209938540973326], [-19.743380539066493, -19.182267540973328], [-19.711287539066518, -19.15455154097333], [-19.679265539066506, -19.12679154097333], [-19.647314539066514, -19.098987540973326], [-19.615434539066513, -19.071138540973323], [-19.583624539066506, -19.04324654097333], [-19.551886539066516, -19.01530954097332], [-19.52021853906652, -18.987328540973323], [-19.488621539066514, -18.959303540973323], [-19.4570955390665, -18.93123554097332], [-19.42563953906651, -18.903122540973328], [-19.394255539066506, -18.87496654097332], [-19.362941539066497, -18.846767540973318], [-19.331699539066506, -18.81852354097333], [-19.300527539066508, -18.790236540973325], [-19.2694275390665, -18.761906540973328], [-19.23839753906651, -18.73353254097333], [-19.207438539066516, -18.705115540973324], [-19.17655053906651, -18.67665554097333], [-19.145733539066498, -18.648152540973328], [-19.114987539066504, -18.619605540973325], [-19.0843135390665, -18.59101554097333], [-19.053709539066517, -18.56238354097333], [-19.023176539066498, -18.533707540973325], [-18.992714539066498, -18.504989540973327], [-18.962323539066517, -18.476228540973324], [-18.9320035390665, -18.44742454097333], [-18.901754539066502, -18.41857754097333], [-18.871576539066496, -18.389688540973324], [-18.84146953906651, -18.360756540973327], [-18.811433539066513, -18.33178254097332], [-18.78146853906651, -18.302765540973326], [-18.751574539066496, -18.273706540973322], [-18.7217525390665, -18.244604540973327], [-18.6920005390665, -18.215460540973325], [-18.662319539066516, -18.18627454097333], [-18.632709539066497, -18.157046540973326], [-18.603170539066497, -18.127775540973317], [-18.573702539066517, -18.09846254097333], [-18.5443055390665, -18.069108540973318], [-18.514979539066502, -18.03971154097333], [-18.4857235390665, -18.01027354097333], [-18.45653953906651, -17.980792540973326], [-18.427426539066516, -17.951270540973326], [-18.398384539066512, -17.921706540973318], [-18.369412539066502, -17.89210054097333], [-18.34051253906651, -17.862452540973322], [-18.31168253906651, -17.832763540973318], [-18.282923539066502, -17.80303254097332], [-18.254235539066514, -17.773259540973328], [-18.225619539066514, -17.743445540973326], [-18.19707253906651, -17.71358954097333], [-18.168597539066496, -17.683692540973325], [-18.1401935390665, -17.653753540973327], [-18.1118595390665, -17.623773540973318], [-18.08359653906652, -17.593752540973327], [-18.0554045390665, -17.56368954097333], [-18.027283539066502, -17.53358554097332], [-17.999232539066497, -17.50344054097333], [-17.97125353906651, -17.47325454097333], [-17.943344539066516, -17.44302654097332], [-17.915505539066515, -17.41275754097333], [-17.887738539066504, -17.38244854097333], [-17.860041539066515, -17.35209754097332], [-17.832415539066517, -17.321705540973326], [-17.804859539066513, -17.291272540973324], [-17.7773745390665, -17.260798540973326], [-17.749960539066507, -17.230283540973318], [-17.722616539066507, -17.199727540973328], [-17.6953435390665, -17.169130540973327], [-17.668140539066513, -17.138492540973317], [-17.64100853906652, -17.107814540973322], [-17.613947539066515, -17.07709454097332], [-17.586956539066506, -17.04633454097332], [-17.56003553906652, -17.015533540973323], [-17.533185539066494, -16.984692540973327], [-17.506406539066518, -16.953809540973324], [-17.479697539066507, -16.922886540973323], [-17.453058539066518, -16.891922540973326], [-17.426490539066492, -16.86091854097333], [-17.399992539066517, -16.829873540973324], [-17.373564539066507, -16.798787540973322], [-17.347207539066517, -16.76766154097332], [-17.320920539066492, -16.736494540973325], [-17.294703539066518, -16.70528754097333], [-17.268557539066506, -16.674039540973325], [-17.242481539066517, -16.64275154097332], [-17.216475539066494, -16.611422540973322], [-17.190540539066518, -16.580052540973327], [-17.16467453906651, -16.54864254097332], [-17.138879539066494, -16.517192540973326], [-17.1131545390665, -16.485701540973324], [-17.0874995390665, -16.454170540973323], [-17.061914539066493, -16.422599540973323], [-17.036400539066506, -16.390987540973327], [-17.010955539066515, -16.35933454097332], [-16.985580539066518, -16.32764254097333], [-16.960276539066513, -16.29590854097333], [-16.935041539066503, -16.264135540973328], [-16.909877539066514, -16.23232154097333], [-16.884782539066492, -16.20046754097332], [-16.859757539066493, -16.168573540973327], [-16.834803539066513, -16.136638540973323], [-16.8099185390665, -16.10466354097332], [-16.78510353906651, -16.07264854097332], [-16.760358539066516, -16.04059254097332], [-16.735683539066514, -16.008496540973326], [-16.71107753906651, -15.976360540973317], [-16.686542539066494, -15.944184540973325], [-16.662076539066504, -15.911967540973322], [-16.63768053906651, -15.87971054097332], [-16.61335353906651, -15.84741354097332], [-16.589096539066503, -15.815075540973325], [-16.56490953906652, -15.782698540973328], [-16.5407925390665, -15.750280540973321], [-16.516744539066508, -15.71782254097333], [-16.49276653906651, -15.685323540973329], [-16.468858539066503, -15.652784540973329], [-16.445019539066493, -15.62020554097333], [-16.421250539066506, -15.58758654097332], [-16.397550539066515, -15.554927540973324], [-16.373920539066518, -15.522227540973319], [-16.350359539066517, -15.489487540973329], [-16.32686853906651, -15.456707540973326], [-16.3034465390665, -15.423887540973325], [-16.280093539066513, -15.391026540973328], [-16.256810539066493, -15.358125540973319], [-16.233597539066494, -15.325184540973325], [-16.210452539066495, -15.29220254097332], [-16.187378539066515, -15.259180540973318], [-16.164372539066505, -15.226118540973317], [-16.141436539066518, -15.193016540973318], [-16.1185695390665, -15.159873540973322], [-16.095771539066504, -15.126690540973328], [-16.073043539066504, -15.093467540973322], [-16.0503845390665, -15.06020454097333], [-16.02779453906652, -15.02690054097333], [-16.005273539066508, -14.993555540973318], [-15.982821539066492, -14.96017154097332], [-15.960439539066499, -14.926746540973326], [-15.938126539066502, -14.893280540973322], [-15.915881539066504, -14.859775540973331], [-15.8937065390665, -14.826228540973318], [-15.871600539066492, -14.792642540973318], [-15.849563539066509, -14.759015540973323], [-15.827595539066493, -14.725347540973331], [-15.8056975390665, -14.691640540973324], [-15.783867539066506, -14.657891540973324], [-15.762106539066508, -14.624102540973325], [-15.740414539066506, -14.590273540973328], [-15.718791539066501, -14.55640354097332], [-15.697237539066492, -14.52249354097333], [-15.675752539066508, -14.488542540973327], [-15.654336539066492, -14.454551540973327], [-15.6329895390665, -14.42051954097333], [-15.611710539066507, -14.386446540973324], [-15.590501539066508, -14.35233354097332], [-15.569360539066508, -14.318179540973318], [-15.548288539066505, -14.283984540973321], [-15.527285539066497, -14.249749540973326], [-15.506351539066515, -14.21547354097332], [-15.4854865390665, -14.18115754097333], [-15.464689539066512, -14.14679954097332], [-15.443961539066493, -14.112401540973323], [-15.423302539066498, -14.077962540973317], [-15.4027125390665, -14.043483540973327], [-15.3821905390665, -14.008962540973329], [-15.361737539066496, -13.974401540973318], [-15.341353539066517, -13.939799540973326], [-15.32103753906651, -13.905155540973325], [-15.300790539066497, -13.870471540973327], [-15.28061253906651, -13.83574754097333], [-15.260502539066493, -13.800981540973325], [-15.240461539066501, -13.766174540973324], [-15.220488539066508, -13.731326540973328], [-15.200584539066512, -13.69643754097332], [-15.180749539066511, -13.661507540973318], [-15.16098253906651, -13.62653654097332], [-15.141284539066504, -13.591523540973327], [-15.121655539066495, -13.556470540973322], [-15.102094539066513, -13.521375540973324], [-15.082601539066502, -13.48623954097333], [-15.063177539066515, -13.451062540973325], [-15.043822539066497, -13.415844540973325], [-15.024535539066505, -13.38058454097333], [-15.005316539066513, -13.345283540973327], [-14.986167539066514, -13.309941540973327], [-14.967085539066517, -13.27455754097332], [-14.948072539066516, -13.23913254097333], [-14.929128539066511, -13.203665540973319], [-14.910252539066505, -13.168157540973326], [-14.891444539066498, -13.132607540973325], [-14.872705539066516, -13.097016540973328], [-14.854034539066504, -13.061383540973324], [-14.835432539066517, -13.025709540973324], [-14.8168985390665, -12.98999354097333], [-14.798433539066508, -12.954235540973329], [-14.780036539066515, -12.91843554097332], [-14.761707539066492, -12.88259454097333], [-14.743447539066494, -12.846711540973331], [-14.725255539066495, -12.810786540973325], [-14.707132539066492, -12.774819540973326], [-14.689077539066517, -12.738810540973319], [-14.671090539066512, -12.70276054097333], [-14.653172539066503, -12.666667540973322], [-14.635322539066493, -12.63053254097332], [-14.617541539066508, -12.594355540973325], [-14.599828539066493, -12.558136540973322], [-14.582183539066506, -12.521875540973326], [-14.564607539066515, -12.485572540973322], [-14.547099539066494, -12.449227540973325], [-14.5296595390665, -12.412839540973323], [-14.512288539066503, -12.376409540973327], [-14.494986539066502, -12.339937540973324], [-14.477751539066503, -12.30342254097333], [-14.4605855390665, -12.266865540973328], [-14.443488539066493, -12.23026554097332], [-14.426458539066516, -12.19362354097332], [-14.409497539066507, -12.156938540973329], [-14.392605539066494, -12.12021154097333], [-14.375781539066509, -12.083441540973325], [-14.359025539066494, -12.04662854097333], [-14.342338539066503, -12.00977254097333], [-14.325719539066512, -11.972874540973322], [-14.309168539066519, -11.935933540973323], [-14.292686539066494, -11.89894954097332], [-14.276273539066494, -11.861923540973322], [-14.259927539066496, -11.824853540973322], [-14.24365153906652, -11.787740540973317], [-14.227442539066516, -11.750584540973321], [-14.211302539066509, -11.71338554097332], [-14.195231539066498, -11.676143540973328], [-14.179227539066517, -11.638858540973331], [-14.163293539066501, -11.601529540973331], [-14.147427539066513, -11.564158540973324], [-14.131629539066495, -11.52674254097333], [-14.115900539066502, -11.48928454097333], [-14.100239539066507, -11.451782540973326], [-14.084646539066512, -11.414237540973318], [-14.06912353906651, -11.37664854097332], [-14.05366753906651, -11.339015540973321], [-14.038281539066503, -11.30133954097333], [-14.022962539066498, -11.263619540973323], [-14.007713539066515, -11.225855540973328], [-13.992531539066505, -11.188048540973327], [-13.977419539066517, -11.150197540973323], [-13.9623755390665, -11.11230154097332], [-13.94739953906651, -11.074362540973326], [-13.932493539066513, -11.036379540973329], [-13.917654539066518, -10.998352540973329], [-13.902885539066517, -10.960281540973327], [-13.888184539066515, -10.922166540973322], [-13.873552539066509, -10.884006540973317], [-13.858988539066502, -10.845802540973324], [-13.84449353906652, -10.807554540973328], [-13.830067539066505, -10.769261540973318], [-13.815709539066518, -10.73092454097332], [-13.801420539066498, -10.692543540973318], [-13.787200539066504, -10.654117540973317], [-13.773049539066506, -10.61564654097333], [-13.758967539066504, -10.577131540973326], [-13.7449535390665, -10.538571540973322], [-13.731008539066494, -10.499966540973318], [-13.717132539066512, -10.461317540973326], [-13.703325539066498, -10.422622540973322], [-13.68958653906651, -10.38388354097333], [-13.675917539066518, -10.345099540973322], [-13.662316539066495, -10.306269540973318], [-13.648785539066495, -10.267395540973325], [-13.635322539066493, -10.22847554097332], [-13.621929539066514, -10.18951054097333], [-13.608604539066505, -10.150500540973326], [-13.595348539066492, -10.111444540973324], [-13.582162539066502, -10.072343540973321], [-13.56904453906651, -10.033197540973319], [-13.555996539066513, -9.994005540973319], [-13.543017539066511, -9.954768540973319], [-13.530106539066509, -9.915484540973324], [-13.5172655390665, -9.876156540973327], [-13.504494539066513, -9.83678154097332], [-13.491791539066497, -9.797361540973327], [-13.479158539066503, -9.757894540973325], [-13.466594539066506, -9.718382540973323], [-13.454099539066505, -9.678824540973324], [-13.4416735390665, -9.639219540973329], [-13.429317539066517, -9.59956954097332], [-13.417030539066502, -9.55987254097333], [-13.40481353906651, -9.520129540973329], [-13.392665539066513, -9.48034054097333], [-13.38058753906651, -9.440504540973322], [-13.368578539066505, -9.40062254097333], [-13.356638539066495, -9.36069354097333], [-13.344768539066507, -9.320718540973317], [-13.332968539066513, -9.280696540973324], [-13.321237539066516, -9.240627540973321], [-13.309576539066512, -9.200512540973321], [-13.297985539066502, -9.160350540973326], [-13.286463539066517, -9.120141540973322], [-13.275011539066497, -9.079885540973322], [-13.2636295390665, -9.03958154097333], [-13.252317539066496, -8.999231540973327], [-13.241074539066517, -8.958834540973328], [-13.2299025390665, -8.918389540973322], [-13.21879953906651, -8.877897540973322], [-13.207766539066512, -8.837358540973327], [-13.196803539066508, -8.796771540973324], [-13.185911539066495, -8.75613654097333], [-13.175088539066508, -8.715455540973323], [-13.164335539066514, -8.674725540973327], [-13.15365353906651, -8.633948540973321], [-13.143041539066502, -8.593123540973323], [-13.132498539066518, -8.552250540973318], [-13.122027539066494, -8.511329540973321], [-13.111625539066495, -8.470360540973317], [-13.101294539066515, -8.42934354097332], [-13.091033539066501, -8.388278540973317], [-13.08084253906651, -8.347165540973322], [-13.070722539066509, -8.30600454097332], [-13.0606735390665, -8.264794540973327], [-13.050694539066512, -8.223536540973328], [-13.040785539066519, -8.182229540973324], [-13.030948539066515, -8.140874540973329], [-13.021181539066504, -8.099470540973329], [-13.011484539066515, -8.058018540973322], [-13.001858539066518, -8.016516540973328], [-12.992303539066512, -7.974966540973327], [-12.982819539066497, -7.933367540973322], [-12.973406539066502, -7.891719540973327], [-12.964064539066499, -7.8500225409733275], [-12.954793539066515, -7.808276540973324], [-12.945592539066496, -7.766481540973331], [-12.936463539066494, -7.7246365409733215], [-12.927405539066513, -7.682742540973322], [-12.918418539066494, -7.640799540973319], [-12.909502539066494, -7.598806540973328], [-12.900658539066512, -7.556763540973321], [-12.891885539066493, -7.514671540973325], [-12.883183539066493, -7.472529540973326], [-12.874553539066511, -7.430338540973324], [-12.86599453906652, -7.388096540973322], [-12.857506539066492, -7.3458055409733305], [-12.849090539066509, -7.303464540973323], [-12.840746539066515, -7.2610725409733305], [-12.83247453906651, -7.21863154097332], [-12.824273539066496, -7.176139540973324], [-12.8161445390665, -7.1335975409733265], [-12.808086539066494, -7.09100454097333], [-12.800101539066503, -7.048361540973318], [-12.792187539066504, -7.005668540973318], [-12.784346539066519, -6.962924540973319], [-12.776576539066497, -6.920129540973321], [-12.768879539066518, -6.877283540973323], [-12.761254539066499, -6.834387540973324], [-12.753701539066498, -6.791440540973326], [-12.746220539066513, -6.748441540973317], [-12.738812539066515, -6.705392540973321], [-12.731476539066506, -6.662291540973328], [-12.724212539066514, -6.619140540973319], [-12.717021539066508, -6.575936540973331], [-12.709902539066519, -6.532682540973326], [-12.702856539066516, -6.489376540973325], [-12.6958835390665, -6.4460195409733245], [-12.688983539066498, -6.402610540973328], [-12.682155539066514, -6.35914954097332], [-12.675400539066516, -6.31563654097333], [-12.668718539066504, -6.272072540973326], [-12.662109539066506, -6.228456540973326], [-12.655573539066495, -6.184787540973318], [-12.649110539066498, -6.141067540973324], [-12.642721539066514, -6.09729554097332], [-12.636404539066518, -6.053470540973322], [-12.630161539066506, -6.009593540973327], [-12.623991539066509, -5.965663540973324], [-12.617895539066495, -5.921681540973324], [-12.611872539066496, -5.8776465409733305], [-12.60592353906651, -5.833559540973326], [-12.600047539066509, -5.789419540973327], [-12.594245539066492, -5.745227540973318], [-12.588517539066515, -5.700981540973331], [-12.585681539066513, -5.678840540973326], [-12.582862539066497, -5.656682540973321], [-12.580063539066515, -5.634515540973325], [-12.577282539066516, -5.612331540973329], [-12.574520539066498, -5.5901375409733305], [-12.571775539066493, -5.567926540973318], [-12.569050539066495, -5.54570554097333], [-12.566343539066509, -5.523468540973326], [-12.563655539066502, -5.501221540973319], [-12.56098453906651, -5.478957540973326], [-12.558333539066496, -5.45668354097333], [-12.555700539066493, -5.43439254097332], [-12.553086539066499, -5.4120915409733215], [-12.550490539066516, -5.38977454097332], [-12.547913539066514, -5.367446540973319], [-12.545354539066494, -5.345102540973329], [-12.54281553906651, -5.322748540973322], [-12.54029353906651, -5.300377540973329], [-12.537790539066492, -5.277996540973319], [-12.53530653906651, -5.255598540973324], [-12.53284153906651, -5.233190540973325], [-12.530394539066492, -5.210765540973327], [-12.527966539066512, -5.188330540973325], [-12.525556539066514, -5.165879540973322], [-12.523165539066497, -5.143417540973317], [-12.520793539066517, -5.120938540973327], [-12.518439539066492, -5.09844954097332], [-12.516104539066504, -5.075943540973327], [-12.513788539066496, -5.053427540973331], [-12.511491539066498, -5.030895540973319], [-12.50921253906651, -5.00835254097332], [-12.506952539066504, -4.985792540973321], [-12.504711539066506, -4.9632225409733195], [-12.502488539066519, -4.940635540973318], [-12.50028553906651, -4.91803754097333], [-12.498100539066513, -4.895423540973326], [-12.495934539066496, -4.872798540973321], [-12.49378653906652, -4.850157540973328], [-12.491658539066492, -4.82750554097332], [-12.489548539066504, -4.804837540973324], [-12.487457539066497, -4.78215754097333], [-12.485385539066499, -4.759461540973319], [-12.483331539066512, -4.73675554097332], [-12.481297539066503, -4.714032540973321], [-12.479281539066506, -4.691298540973321], [-12.477284539066517, -4.6685475409733215], [-12.475307539066506, -4.645786540973319], [-12.473348539066507, -4.623008540973331], [-12.471408539066516, -4.6002195409733275], [-12.469486539066509, -4.577413540973325], [-12.467584539066507, -4.554597540973319], [-12.465701539066515, -4.531764540973327], [-12.463836539066506, -4.508920540973321], [-12.461991539066503, -4.486059540973329], [-12.460164539066511, -4.46318854097332], [-12.4583565390665, -4.440299540973328], [-12.456568539066495, -4.417400540973318], [-12.454798539066502, -4.394484540973323], [-12.453048539066515, -4.371557540973328], [-12.45131653906651, -4.34861454097333], [-12.449603539066516, -4.325659540973319], [-12.447910539066498, -4.302688540973321], [-12.446235539066492, -4.279706540973322], [-12.444580539066493, -4.2567075409733235], [-12.442943539066505, -4.233696540973327], [-12.441326539066495, -4.210670540973325], [-12.439727539066496, -4.1876325409733255], [-12.438148539066503, -4.164577540973326], [-12.43658853906652, -4.141511540973326], [-12.435047539066517, -4.118428540973326], [-12.433525539066494, -4.095334540973326], [-12.432022539066509, -4.072224540973323], [-12.430538539066504, -4.049102540973323], [-12.429074539066505, -4.025963540973322], [-12.427628539066518, -4.0028145409733185], [-12.426202539066509, -3.9796475409733176], [-12.424795539066508, -3.9564695409733304], [-12.423407539066517, -3.933274540973329], [-12.422038539066506, -3.9100685409733273], [-12.420689539066501, -3.8868465409733233], [-12.419358539066508, -3.863612540973321], [-12.418047539066492, -3.840361540973319], [-12.416756539066512, -3.817098540973319], [-12.415483539066514, -3.793819540973331], [-12.414230539066494, -3.770529540973328], [-12.412996539066512, -3.747221540973328], [-12.41178153906651, -3.7239025409733273], [-12.410585539066517, -3.7005675409733243], [-12.409409539066502, -3.6772195409733257], [-12.408252539066496, -3.653855540973325], [-12.407115539066496, -3.6304805409733234], [-12.405997539066504, -3.6070875409733247], [-12.404898539066494, -3.583684540973323], [-12.403818539066492, -3.560263540973324], [-12.402758539066497, -3.5368305409733267], [-12.40171753906651, -3.5133815409733273], [-12.400696539066502, -3.48992054097333], [-12.399694539066502, -3.4664425409733184], [-12.398711539066511, -3.4429535409733205], [-12.397748539066498, -3.419447540973323], [-12.39680553906652, -3.395929540973327], [-12.395880539066496, -3.3723945409733176], [-12.394976539066505, -3.348847540973324], [-12.394090539066497, -3.3252845409733283], [-12.393224539066495, -3.3017085409733227], [-12.392378539066499, -3.278116540973329], [-12.391551539066512, -3.254512540973323], [-12.390744539066503, -3.2308915409733174], [-12.389956539066503, -3.207258540973328], [-12.38918853906651, -3.183609540973322], [-12.388439539066496, -3.15994754097332], [-12.387710539066518, -3.1362695409733305], [-12.38700053906652, -3.112578540973331], [-12.3863105390665, -3.0888715409733294], [-12.385639539066517, -3.0651525409733296], [-12.384988539066512, -3.0414155409733183], [-12.384357539066514, -3.0176675409733207], [-12.383746539066493, -2.9939025409733233], [-12.38315453906651, -2.970125540973328], [-12.382581539066507, -2.9463315409733184], [-12.382029539066508, -2.922525540973325], [-12.381495539066492, -2.8987015409733203], [-12.380982539066508, -2.874866540973329], [-12.380488539066505, -2.851014540973324], [-12.380015539066505, -2.8271495409733234], [-12.379560539066517, -2.8032685409733205], [-12.379126539066505, -2.7793755409733194], [-12.3787115390665, -2.755464540973321], [-12.378114539066502, -2.726778540973328], [-12.377656539066493, -2.7036475409733214], [-12.377217539066493, -2.680532540973317], [-12.376799539066496, -2.6574295409733253], [-12.376401539066507, -2.634341540973324], [-12.376024539066492, -2.6112655409733208], [-12.375666539066515, -2.58820554097332], [-12.375329539066513, -2.565157540973331], [-12.375012539066518, -2.542124540973319], [-12.3747155390665, -2.5191045409733306], [-12.374439539066515, -2.4960995409733187], [-12.37418253906651, -2.4731055409733216], [-12.373946539066509, -2.450128540973324], [-12.373730539066514, -2.42716154097333], [-12.373534539066497, -2.4042115409733213], [-12.373358539066516, -2.381273540973325], [-12.373202539066511, -2.358350540973319], [-12.373066539066514, -2.3354385409733283], [-12.37295153906652, -2.312543540973323], [-12.372855539066506, -2.2896585409733206], [-12.3727795390665, -2.266790540973318], [-12.372724539066496, -2.2439335409733303], [-12.372688539066502, -2.2210925409733306], [-12.372673539066511, -2.1982625409733174], [-12.372678539066499, -2.1754485409733206], [-12.372702539066495, -2.1526455409733245], [-12.372747539066495, -2.1298585409733306], [-12.372811539066504, -2.1070835409733206], [-12.372896539066517, -2.0843235409733296], [-12.37300053906651, -2.061574540973325], [-12.37312453906651, -2.0388415409733227], [-12.373269539066513, -2.0161205409733185], [-12.373433539066497, -1.993414540973319], [-12.373617539066515, -1.9707195409733202], [-12.373821539066512, -1.9480405409733237], [-12.374045539066515, -1.9253725409733278], [-12.374289539066496, -1.9027205409733199], [-12.374552539066514, -1.8800795409733269], [-12.374836539066507, -1.8574545409733219], [-12.37513953906651, -1.8348405409733175], [-12.375462539066518, -1.812241540973318], [-12.375805539066505, -1.7896545409733307], [-12.376168539066498, -1.7670825409733197], [-12.3765505390665, -1.7445215409733237], [-12.376952539066508, -1.7219765409733299], [-12.377374539066494, -1.6994425409733225], [-12.377816539066515, -1.6769245409733173], [-12.378278539066514, -1.6544165409733296], [-12.378759539066493, -1.6319255409733273], [-12.379260539066507, -1.6094445409733282], [-12.379780539066502, -1.5869795409733172], [-12.3803215390665, -1.5645245409733235], [-12.380881539066507, -1.5420865409733295], [-12.381461539066493, -1.5196585409733245], [-12.382060539066515, -1.4972465409733218], [-12.382679539066515, -1.4748445409733222], [-12.383318539066494, -1.4524595409733223], [-12.38397653906651, -1.4300845409733256], [-12.384654539066503, -1.4077245409733194], [-12.385352539066503, -1.3853765409733256], [-12.386069539066511, -1.3630435409733224], [-12.3868055390665, -1.3407205409733223], [-12.387562539066494, -1.318414540973322], [-12.388338539066496, -1.2961185409733247], [-12.389133539066506, -1.273837540973318], [-12.389948539066495, -1.2515675409733262], [-12.390782539066493, -1.2293135409733225], [-12.391636539066496, -1.2070695409733219], [-12.392510539066507, -1.184842540973321], [-12.393403539066497, -1.1626245409733258], [-12.394316539066494, -1.1404225409733186], [-12.3952485390665, -1.1182315409733263], [-12.396199539066515, -1.0960555409733246], [-12.397170539066508, -1.0738905409733235], [-12.39816053906651, -1.0517405409733271], [-12.399170539066517, -1.0296005409733198], [-12.400199539066506, -1.0074775409733263], [-12.4012485390665, -0.9853635409733243], [-12.402316539066504, -0.9632665409733221], [-12.403404539066514, -0.9411785409733255], [-12.404510539066507, -0.9191065409733312], [-12.405637539066504, -0.8970455409733233], [-12.406782539066512, -0.8749995409733202], [-12.407947539066498, -0.8529635409733203], [-12.409131539066493, -0.8309435409733226], [-12.410335539066494, -0.808933540973328], [-12.411558539066505, -0.786938540973324], [-12.412800539066495, -0.7649545409733207], [-12.414062539066492, -0.7429865409733196], [-12.415343539066498, -0.7210275409733242], [-12.416643539066513, -0.6990845409733311], [-12.417962539066508, -0.6771515409733269], [-12.41930153906651, -0.6552345409733249], [-12.42065953906652, -0.6333275409733261], [-12.42203653906651, -0.6114355409733179], [-12.423433539066508, -0.589553540973327], [-12.424848539066517, -0.5676875409733242], [-12.426283539066503, -0.5458315409733245], [-12.427737539066499, -0.5239915409733271], [-12.4292115390665, -0.5021605409733212], [-12.430703539066513, -0.4803455409733175], [-12.432215539066505, -0.4585405409733312], [-12.433745539066507, -0.4367505409733212], [-12.435295539066516, -0.41497054097332864], [-12.436864539066505, -0.3932065409733241], [-12.4384535390665, -0.3714525409733227], [-12.440060539066508, -0.3497135409733261], [-12.441687539066493, -0.3279845409733184], [-12.443332539066517, -0.30627054097332973], [-12.444997539066492, -0.28456654097333], [-12.446681539066503, -0.2628785409733183], [-12.448384539066495, -0.24119954097332652], [-12.450105539066499, -0.21953654097332276], [-12.451847539066506, -0.19788354097332217], [-12.453607539066496, -0.17624554097332634], [-12.455386539066495, -0.15461754097331948], [-12.457184539066503, -0.13300454097331738], [-12.459001539066492, -0.11140154097331845], [-12.460837539066517, -0.08981354097332428], [-12.462692539066495, -0.06823554097331908], [-12.46456653906651, -0.04667354097333032], [-12.466460539066503, -0.02512054097331884], [-12.468372539066507, -0.0035825409733263314], [-12.470303539066492, 0.017945459026677213], [-12.472253539066514, 0.03945745902667852], [-12.474222539066517, 0.060961459026671605], [-12.4762105390665, 0.08244845902667919], [-12.478217539066492, 0.10392745902667855], [-12.480243539066493, 0.1253894590266782], [-12.482288539066502, 0.14684345902666962], [-12.484351539066495, 0.16828045902667554], [-12.486434539066494, 0.18970945902667324], [-12.488535539066504, 0.2111224590266687], [-12.490656539066492, 0.23252645902667268], [-12.492795539066492, 0.2539144590266744], [-12.4949535390665, 0.27529345902667046], [-12.497130539066518, 0.29665745902667595], [-12.499326539066516, 0.31801145902667827], [-12.501540539066497, 0.3393504590266758], [-12.503774539066512, 0.3606804590266819], [-12.50602653906651, 0.3819944590266715], [-12.508297539066518, 0.40329945902666964], [-12.510587539066506, 0.4245894590266772], [-12.512896539066503, 0.4458704590266791], [-12.515223539066511, 0.46713545902667875], [-12.517570539066497, 0.4883914590266727], [-12.519934539066497, 0.5096314590266786], [-12.522318539066504, 0.5308634590266763], [-12.524721539066519, 0.5520794590266718], [-12.527142539066517, 0.5732864590266757], [-12.529582539066496, 0.594478459026675], [-12.532041539066512, 0.615660459026671], [-12.53451853906651, 0.636828459026674], [-12.537015539066516, 0.6579864590266737], [-12.539529539066507, 0.6791294590266688], [-12.542063539066504, 0.7002634590266723], [-12.544615539066513, 0.7213824590266711], [-12.547186539066502, 0.7424914590266809], [-12.5497765390665, 0.7635864590266692], [-12.552384539066509, 0.7846714590266828], [-12.555011539066498, 0.8057414590266774], [-12.557657539066497, 0.826803459026678], [-12.560321539066507, 0.8478494590266763], [-12.563004539066498, 0.868886459026669], [-12.5657055390665, 0.8899074590266736], [-12.568426539066508, 0.9109214590266816], [-12.571164539066501, 0.9319184590266758], [-12.573922539066501, 0.952907459026676], [-12.576697539066515, 0.9738814590266713], [-12.579492539066507, 0.9948464590266752], [-12.58230553906651, 1.015795459026677], [-12.585137539066494, 1.0367364590266703], [-12.587987539066518, 1.0576624590266732], [-12.590856539066493, 1.0785794590266704], [-12.593743539066509, 1.0994804590266796], [-12.596649539066505, 1.120374459026678], [-12.599573539066512, 1.1412514590266767], [-12.602517539066497, 1.1621214590266788], [-12.605478539066496, 1.1829744590266813], [-12.608458539066504, 1.203820459026673], [-12.611456539066495, 1.2246504590266767], [-12.614473539066495, 1.2454724590266721], [-12.617509539066504, 1.2662784590266796], [-12.620563539066495, 1.2870764590266788], [-12.623635539066498, 1.3078584590266757], [-12.62672653906651, 1.3286324590266787], [-12.629835539066505, 1.349391459026677], [-12.632963539066509, 1.370142459026681], [-12.636109539066496, 1.3908774590266688], [-12.63927453906652, 1.4116044590266767], [-12.642457539066498, 1.4323154590266824], [-12.645659539066514, 1.45301845902668], [-12.648879539066513, 1.4737064590266726], [-12.652117539066495, 1.4943864590266713], [-12.655374539066514, 1.515050459026682], [-12.658649539066516, 1.5357064590266702], [-12.661942539066501, 1.5563474590266821], [-12.665255539066493, 1.5769804590266716], [-12.668585539066498, 1.597597459026673], [-12.671934539066513, 1.618207459026678], [-12.67530153906651, 1.638800459026669], [-12.678686539066518, 1.6593864590266776], [-12.682090539066508, 1.6799574590266815], [-12.685512539066508, 1.7005194590266797], [-12.68895253906652, 1.721066459026673], [-12.692411539066512, 1.74160645902667], [-12.695888539066516, 1.7621304590266789], [-12.6993845390665, 1.7826464590266795], [-12.702897539066498, 1.803146459026678], [-12.706430539066503, 1.8236394590266798], [-12.709980539066493, 1.8441164590266794], [-12.71354953906652, 1.8645864590266825], [-12.717135539066504, 1.8850404590266692], [-12.720741539066495, 1.905486459026676], [-12.7243645390665, 1.925917459026678], [-12.728006539066513, 1.9463414590266694], [-12.73166653906651, 1.9667484590266753], [-12.735344539066517, 1.987149459026682], [-12.739040539066508, 2.007533459026675], [-12.742755539066508, 2.027910459026671], [-12.746488539066519, 2.048272459026677], [-12.75024053906651, 2.0686264590266745], [-12.754009539066516, 2.0889654590266815], [-12.757797539066502, 2.1092964590266803], [-12.761602539066502, 2.1296124590266743], [-12.76542653906651, 2.1499204590266743], [-12.769268539066502, 2.1702134590266695], [-12.773129539066503, 2.1904984590266707], [-12.777007539066517, 2.2107684590266814], [-12.78090553906651, 2.2310314590266813], [-12.784819539066518, 2.2512774590266815], [-12.788753539066505, 2.2715174590266827], [-12.792704539066506, 2.2917414590266816], [-12.796673539066518, 2.3119584590266697], [-12.80066153906651, 2.3321604590266816], [-12.804667539066514, 2.352354459026671], [-12.808690539066504, 2.37253345902667], [-12.8127335390665, 2.3927044590266746], [-12.81679353906651, 2.4128604590266747], [-12.820871539066502, 2.433009459026678], [-12.824967539066506, 2.4531424590266795], [-12.829082539066519, 2.47326845902667], [-12.833214539066518, 2.49337945902667], [-12.837366539066494, 2.5134834590266735], [-12.841534539066515, 2.5335714590266747], [-12.845721539066517, 2.5536524590266794], [-12.849926539066502, 2.573717459026682], [-12.854150539066495, 2.593776459026671], [-12.858390539066505, 2.613819459026672], [-12.862650539066493, 2.6338554590266767], [-12.866927539066495, 2.653875459026679], [-12.871223539066506, 2.6738894590266824], [-12.875536539066502, 2.6938874590266693], [-12.879868539066507, 2.713878459026674], [-12.884217539066498, 2.7338544590266736], [-12.888585539066497, 2.753823459026677], [-12.89297053906651, 2.773776459026678], [-12.897374539066504, 2.7937224590266823], [-12.901795539066512, 2.813653459026682], [-12.9062355390665, 2.8335784590266826], [-12.910692539066503, 2.8534864590266693], [-12.915168539066514, 2.873388459026671], [-12.919662539066508, 2.893274459026671], [-12.924174539066513, 2.9131544590266714], [-12.928703539066504, 2.9330184590266697], [-12.933251539066504, 2.952876459026669], [-12.937816539066517, 2.97271845902668], [-12.942400539066512, 2.9925534590266807], [-12.947002539066517, 3.0123734590266764], [-12.951622539066506, 3.0321864590266756], [-12.956259539066508, 3.05198445902667], [-12.96091553906652, 3.071775459026682], [-12.965588539066516, 3.0915514590266753], [-12.970280539066493, 3.111320459026672], [-12.974988539066516, 3.1310734590266804], [-12.979716539066516, 3.150821459026673], [-12.984461539066501, 3.1705524590266805], [-12.989225539066496, 3.1902774590266745], [-12.994005539066507, 3.209987459026678], [-12.998805539066495, 3.2296904590266706], [-13.0036215390665, 3.2493784590266728], [-13.008457539066512, 3.2690594590266784], [-13.013309539066512, 3.2887254590266792], [-13.018180539066492, 3.3083844590266693], [-13.023068539066514, 3.328028459026669], [-13.027975539066517, 3.3476664590266694], [-13.032899539066506, 3.367288459026682], [-13.037842539066503, 3.386904459026681], [-13.042802539066514, 3.406504459026678], [-13.047780539066508, 3.426098459026676], [-13.052776539066514, 3.4456764590266715], [-13.057790539066502, 3.46524945902668], [-13.062821539066505, 3.484805459026674], [-13.067871539066516, 3.504356459026681], [-13.072938539066513, 3.5238914590266717], [-13.078024539066519, 3.5434204590266773], [-13.08312753906651, 3.562933459026681], [-13.088248539066512, 3.5824414590266827], [-13.0933865390665, 3.6019334590266823], [-13.098544539066495, 3.621418459026671], [-13.103718539066506, 3.6408884590266695], [-13.108911539066497, 3.6603534590266804], [-13.114120539066505, 3.6798014590266774], [-13.11934953906652, 3.699244459026673], [-13.124594539066493, 3.7186714590266803], [-13.129858539066504, 3.7380924590266744], [-13.1351395390665, 3.757498459026678], [-13.140439539066506, 3.7768984590266825], [-13.145756539066497, 3.7962824590266706], [-13.151091539066499, 3.815660459026674], [-13.156443539066515, 3.8350234590266723], [-13.16181553906651, 3.8543804590266717], [-13.167202539066494, 3.873721459026669], [-13.172609539066514, 3.8930574590266787], [-13.178032539066493, 3.9123764590266745], [-13.183475539066507, 3.9316914590266805], [-13.188933539066511, 3.9509894590266725], [-13.19441253906652, 3.970282459026677], [-13.199906539066518, 3.989560459026677], [-13.205419539066497, 4.0088314590266805], [-13.210949539066519, 4.028087459026679], [-13.216498539066492, 4.047338459026676], [-13.222064539066508, 4.066573459026671], [-13.227649539066505, 4.085802459026681], [-13.233249539066492, 4.105016459026672], [-13.238870539066511, 4.124224459026678], [-13.244506539066492, 4.143416459026682], [-13.250162539066508, 4.1626044590266815], [-13.255834539066512, 4.181775459026682], [-13.261525539066497, 4.20094145902668], [-13.267232539066498, 4.220091459026676], [-13.272959539066505, 4.239236459026671], [-13.2787025390665, 4.2583654590266775], [-13.284464539066505, 4.2774894590266825], [-13.290242539066497, 4.296597459026671], [-13.296040539066496, 4.315700459026672], [-13.301854539066511, 4.334787459026671], [-13.307687539066507, 4.353869459026683], [-13.313536539066519, 4.3729364590266755], [-13.319405539066508, 4.391997459026669], [-13.325289539066517, 4.411042459026675], [-13.331193539066504, 4.4300824590266785], [-13.337113539066507, 4.44910645902668], [-13.343053539066517, 4.468126459026678], [-13.349008539066517, 4.487129459026676], [-13.354983539066495, 4.5061284590266695], [-13.360974539066518, 4.525110459026678], [-13.366984539066493, 4.544088459026682], [-13.373010539066513, 4.56305045902667], [-13.37905653906651, 4.58200745902667], [-13.385118539066497, 4.600948459026682], [-13.39119953906652, 4.619884459026679], [-13.397296539066502, 4.638804459026673], [-13.403412539066494, 4.657720459026677], [-13.4095455390665, 4.676619459026682], [-13.415696539066516, 4.695514459026683], [-13.421864539066519, 4.714393459026681], [-13.428051539066502, 4.733267459026678], [-13.434254539066501, 4.752125459026672], [-13.440477539066507, 4.770979459026677], [-13.446715539066503, 4.789816459026682], [-13.452973539066505, 4.808649459026682], [-13.459247539066496, 4.827466459026681], [-13.465540539066495, 4.846278459026678], [-13.471849539066511, 4.86507545902667], [-13.478178539066505, 4.883867459026675], [-13.484522539066518, 4.902643459026677], [-13.490886539066508, 4.921414459026678], [-13.497265539066518, 4.940169459026677], [-13.503665539066503, 4.958920459026672], [-13.510080539066507, 4.977655459026678], [-13.516514539066492, 4.996386459026681], [-13.522964539066493, 5.0151004590266695], [-13.5294345390665, 5.033810459026682], [-13.535920539066495, 5.052504459026679], [-13.5424255390665, 5.071194459026671], [-13.548946539066492, 5.089868459026675], [-13.555486539066493, 5.108537459026678], [-13.56204253906651, 5.127190459026679], [-13.568618539066506, 5.145839459026675], [-13.575209539066492, 5.164472459026669], [-13.581820539066513,
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
